DisheveledDev/SPIConputer/system/audio.c

/* audio.c — see audio.h */
#include "audio.h"

#include <math.h>
#include "mod.h"
#include <stdlib.h>
#include <string.h>

audio_state_t *g_current_audio;

/* ------------------------------------------------------------------ */
/* Fixed-point tables (built once, using double math)                  */
/* ------------------------------------------------------------------ */

enum { AUDIO_BLOCK = 64 };

static bool s_tables_ready;
static uint32_t s_note_inc[128];   /* tone phase increment, Q32/sample */
static uint64_t s_pitch_q32[128];  /* 2^((n-60)/12), Q32 (sample pitch) */
static int16_t s_sine[256];
static uint32_t s_cent_q16[100];   /* 2^(c/1200), Q16: a fraction of a semitone */

static void build_tables(void) {
    if (s_tables_ready) {
        return;
    }
    for (int n = 0; n < 128; n++) {
        double freq = 440.0 * pow(2.0, (n - 69) / 12.0);
        s_note_inc[n] =
            (uint32_t)llround(freq / AUDIO_SAMPLE_RATE * 4294967296.0);
        s_pitch_q32[n] = (uint64_t)llround(pow(2.0, (n - 60) / 12.0) * 4294967296.0);
    }
    for (int i = 0; i < 256; i++) {
        s_sine[i] = (int16_t)lround(sin(2.0 * 3.14159265358979323846 * i / 256.0) *
                                    32767.0);
    }
    for (int c = 0; c < 100; c++) {
        s_cent_q16[c] = (uint32_t)llround(pow(2.0, c / 1200.0) * 65536.0);
    }
    s_tables_ready = true;
}

static uint64_t ms_to_frames(uint32_t ms) {
    return (uint64_t)ms * AUDIO_SAMPLE_RATE / 1000u;
}

/* ------------------------------------------------------------------ */
/* Note names                                                          */
/* ------------------------------------------------------------------ */

int audio_note_parse(const char *name) {
    if (!name || !name[0]) {
        return -1;
    }
    char c = name[0];
    if (c >= 'a' && c <= 'g') {
        c = (char)(c - 'a' + 'A');
    }
    static const int base[7] = {9, 11, 0, 2, 4, 5, 7}; /* A B C D E F G */
    if (c < 'A' || c > 'G') {
        return -1;
    }
    int i = 1;
    int semitone = base[c - 'A'];
    if (name[i] == '#') {
        semitone++;
        i++;
    } else if (name[i] == 'b') {
        semitone--;
        i++;
    }
    if (!name[i]) {
        return -1;
    }
    int sign = 1;
    if (name[i] == '-') {
        sign = -1;
        i++;
    }
    if (name[i] < '0' || name[i] > '9') {
        return -1;
    }
    int octave = name[i] - '0';
    i++;
    if (name[i] >= '0' && name[i] <= '9') {
        octave = octave * 10 + (name[i] - '0');
        i++;
    }
    if (name[i] != '\0') {
        return -1;
    }
    octave *= sign;
    int midi = (octave + 1) * 12 + semitone;
    if (midi < 0 || midi > 127) {
        return -1;
    }
    return midi;
}

/* ------------------------------------------------------------------ */
/* State lifetime                                                      */
/* ------------------------------------------------------------------ */

/* Analyser bands: two-pole resonators y = c1*y1 - c2*y2 + g*x at a
 * quarter of the sample rate (11025 Hz), Q of 2.5, unity gain at the
 * centre; Q14. Computed offline: w = 2*pi*fc/fs, r = exp(-pi*fc/(2.5*fs)),
 * c1 = 2*r*cos(w), c2 = r*r, g = (1-r)*sqrt(1 - 2*r*cos(2w) + r*r). */
const uint16_t audio_spectrum_hz[AUDIO_SPECTRUM_BANDS] = {
    60, 100, 160, 250, 400, 630, 1000, 1600, 2500, 4000,
};
static const int32_t s_spec_coef[AUDIO_SPECTRUM_BANDS][3] = {
    {32526, 16161, 8},     {32344, 16015, 21},   {32042, 15797, 54},
    {31525, 15476, 130},   {30498, 14956, 324},  {28553, 14192, 774},
    {24617, 13044, 1809},  {16719, 11377, 3969}, {3586, 9266, 7043},
    {-13520, 6583, 7577},
};

void audio_state_init(audio_state_t *a) {
    memset(a, 0, sizeof(*a));
    a->master = AUDIO_DEFAULT_VOLUME;
    for (int b = 0; b < AUDIO_SPECTRUM_BANDS; b++) {
        a->spec_c1[b] = s_spec_coef[b][0];
        a->spec_c2[b] = s_spec_coef[b][1];
        a->spec_g[b] = s_spec_coef[b][2];
    }
    build_tables();
}

void audio_spectrum(const audio_state_t *a, uint8_t out[AUDIO_SPECTRUM_BANDS]) {
    for (int b = 0; b < AUDIO_SPECTRUM_BANDS; b++) {
        /* Music spreads over the bands, so a band rarely nears the
         * full-scale-sine peak: four times the raw level (a centred
         * full-scale tone saturates) less a floor that hides the low
         * bands' rounding ripple. */
        uint32_t v = a ? a->spec_level[b] : 0;
        v = v > 512 ? (v - 512) >> 5 : 0;
        out[b] = (uint8_t)(v > 255 ? 255 : v);
    }
}

/* One decimated frame through the resonators (producer). */
static inline void spectrum_feed(audio_state_t *a, int32_t x) {
    for (int b = 0; b < AUDIO_SPECTRUM_BANDS; b++) {
        int32_t y = (int32_t)(((int64_t)a->spec_c1[b] * a->spec_y1[b] -
                               (int64_t)a->spec_c2[b] * a->spec_y2[b] +
                               (int64_t)a->spec_g[b] * x) >> 14);
        a->spec_y2[b] = a->spec_y1[b];
        a->spec_y1[b] = y;
        if (y < 0) y = -y;
        if (y > a->spec_peak[b]) a->spec_peak[b] = y;
    }
}

/* End of a block: the levels take the block's peaks and decay by 1/32
 * a block (about 50 ms to fall by two thirds), so a reader polling a
 * few times a frame sees an envelope, not the odd sample. */
static inline void spectrum_block(audio_state_t *a) {
    for (int b = 0; b < AUDIO_SPECTRUM_BANDS; b++) {
        int32_t lvl = a->spec_level[b];
        lvl -= lvl >> 5;
        int32_t peak = a->spec_peak[b] > 32767 ? 32767 : a->spec_peak[b];
        if (peak > lvl) lvl = peak;
        a->spec_level[b] = (uint16_t)lvl;
        a->spec_peak[b] = 0;
    }
}

void audio_state_free(audio_state_t *a) {
    free(a->sample_pool);
    a->sample_pool = NULL;
    mod_free(a->mod);
    a->mod = NULL;
}

void audio_service(void) {
    audio_state_t *a = g_current_audio;
    if (a && a->mod) {
        mod_service(a->mod);
    }
}

bool audio_sound_defined(const audio_state_t *a, int sound) {
    if (sound < 0) {
        return false;
    }
    if (sound < AUDIO_INSTRUMENT_MAX) {
        return a->instruments[sound].defined != 0;
    }
    if (sound < AUDIO_INSTRUMENT_MAX + AUDIO_SAMPLE_MAX) {
        return a->samples[sound - AUDIO_INSTRUMENT_MAX].defined != 0;
    }
    if (sound >= AUDIO_PRESET_BASE && sound < AUDIO_PRESET_BASE + audio_preset_count()) {
        return true;
    }
    return false;
}

const audio_instrument_t *audio_instrument(const audio_state_t *a, int sound) {
    if (sound >= 0 && sound < AUDIO_INSTRUMENT_MAX) {
        return a->instruments[sound].defined ? &a->instruments[sound] : NULL;
    }
    if (sound >= AUDIO_PRESET_BASE && sound < AUDIO_PRESET_BASE + audio_preset_count()) {
        return &audio_preset(sound - AUDIO_PRESET_BASE)->ins;
    }
    return NULL;
}

static inline bool is_sample(int sound) {
    return sound >= AUDIO_INSTRUMENT_MAX && sound < AUDIO_INSTRUMENT_MAX + AUDIO_SAMPLE_MAX;
}

/* ------------------------------------------------------------------ */
/* Playback requests (core 1 side)                                     */
/* ------------------------------------------------------------------ */

void audio_play_score(audio_state_t *a, int score, int loop) {
    if (score < 0 || score >= AUDIO_SCORE_MAX) {
        return;
    }
    a->req_score = (uint8_t)score;
    a->req_loop = loop < 0 ? a->scores[score].loop : (uint8_t)(loop != 0);
    a->req_play = 1;
}

void audio_stop_score(audio_state_t *a) {
    a->req_stop = 1;
}

bool audio_score_playing(const audio_state_t *a) {
    if (a->req_stop) {
        return false;
    }
    return a->score_active != 0 || a->req_play != 0;
}

int audio_trigger(audio_state_t *a, int sound, int note, int volume, int pan,
                  int dur_ms) {
    if (!audio_sound_defined(a, sound)) {
        return -1;
    }
    unsigned head = atomic_load_explicit(&a->trig_head, memory_order_relaxed);
    unsigned tail = atomic_load_explicit(&a->trig_tail, memory_order_acquire);
    if ((head + 1) % AUDIO_ONESHOT_VOICES == tail) {
        return -1; /* ring full */
    }
    int slot = (int)head;
    audio_trigger_t *t = &a->trig[slot];
    t->sound = (uint8_t)sound;
    t->note = (uint8_t)(note < 0 ? 0 : (note > 127 ? 127 : note));
    t->volume = (uint8_t)(volume < 0 ? 0 : (volume > 255 ? 255 : volume));
    t->pan = (int8_t)(pan < -64 ? -64 : (pan > 63 ? 63 : pan));
    t->dur_ms = (uint16_t)(dur_ms < 0 ? 0 : (dur_ms > 65535 ? 65535 : dur_ms));
    atomic_store_explicit(&a->trig_head,
                          (head + 1) % AUDIO_ONESHOT_VOICES,
                          memory_order_release);
    return slot;
}

void audio_stop_voice(audio_state_t *a, int slot) {
    if (slot < 0 || slot >= AUDIO_ONESHOT_VOICES) {
        return;
    }
    a->stop_flags[slot] = 1;
}

void audio_stop_all_voices(audio_state_t *a) {
    for (int i = 0; i < AUDIO_ONESHOT_VOICES; i++) {
        a->stop_flags[i] = 1;
    }
}

void audio_pause(audio_state_t *a) {
    for (int i = 0; i < AUDIO_VOICES; i++) {
        a->voices[i].active = 0;
        a->voices[i].env_state = AUDIO_ENV_OFF;
    }
    mod_pause(a->mod);
}

/* ------------------------------------------------------------------ */
/* Voice triggering                                                    */
/* ------------------------------------------------------------------ */

static const audio_instrument_t s_sample_envelope = {
    .defined = 1,
    .wave = AUDIO_WAVE_SINE,
    .duty = AUDIO_DEFAULT_DUTY,
    .attack_ms = 0,
    .decay_ms = 0,
    .sustain = 255,
    .release_ms = 20,
    .volume = 255,
    .cutoff = AUDIO_CUTOFF_OPEN,
};

static uint32_t oneshot_hold(const audio_instrument_t *ins, uint32_t dur_ms) {
    if (dur_ms > 0) {
        return (uint32_t)ms_to_frames(dur_ms);
    }
    return (uint32_t)(ms_to_frames(ins->attack_ms) + ms_to_frames(ins->decay_ms));
}

uint32_t audio_oneshot_frames(const audio_instrument_t *ins) {
    return (uint32_t)(ms_to_frames(ins->attack_ms) + ms_to_frames(ins->decay_ms));
}

static void env_enter_decay(audio_voice_t *v, const audio_instrument_t *ins) {
    v->env_sustain = (int32_t)ins->sustain * 256;
    uint32_t df = (uint32_t)ms_to_frames(ins->decay_ms);
    if (df == 0 || v->env_level <= v->env_sustain) {
        v->env_level = v->env_sustain;
        v->env_state = AUDIO_ENV_SUSTAIN;
        return;
    }
    v->env_state = AUDIO_ENV_DECAY;
    v->env_rate = (v->env_level - v->env_sustain) / (int32_t)df;
    if (v->env_rate < 1) {
        v->env_rate = 1;
    }
}

static void env_enter_release(audio_voice_t *v, const audio_instrument_t *ins) {
    uint32_t rf = (uint32_t)ms_to_frames(ins->release_ms);
    v->env_state = AUDIO_ENV_RELEASE;
    if (rf == 0 || v->env_level <= 0) {
        v->env_level = 0;
        v->env_state = AUDIO_ENV_OFF;
        v->active = 0;
        return;
    }
    v->env_rate = v->env_level / (int32_t)rf;
    if (v->env_rate < 1) {
        v->env_rate = 1;
    }
}

static void voice_start_tone(audio_voice_t *v, const audio_instrument_t *ins,
                             int note, uint32_t hold) {
    memset(v, 0, sizeof(*v));
    v->active = 1;
    v->source = 0;
    v->note = (uint8_t)note;
    v->inc = s_note_inc[note & 0x7f];
    v->lfsr = (uint16_t)(0x4001 | (note << 4));
    v->hold_frames = hold;
    v->env_sustain = (int32_t)ins->sustain * 256;

    uint32_t af = (uint32_t)ms_to_frames(ins->attack_ms);
    if (af == 0) {
        v->env_level = 65536;
        env_enter_decay(v, ins);
    } else {
        v->env_state = AUDIO_ENV_ATTACK;
        v->env_rate = 65536 / (int32_t)af;
        if (v->env_rate < 1) {
            v->env_rate = 1;
        }
    }
}

static void voice_start_sample(audio_voice_t *v, const audio_pcm_t *smp,
                               int note, uint32_t hold) {
    memset(v, 0, sizeof(*v));
    v->active = 1;
    v->source = 1;
    v->note = (uint8_t)note;
    /* s_pitch_q32[n] is 2^((n-60)/12): the shift from the root note. */
    int root = smp->root ? smp->root : 60;
    int shift = 60 + (note & 0x7f) - root;
    if (shift < 0) shift = 0;
    if (shift > 127) shift = 127;
    v->step = ((uint64_t)smp->rate * s_pitch_q32[shift]) / AUDIO_SAMPLE_RATE;
    v->hold_frames = hold;
    v->env_sustain = 65536;
    v->env_level = 65536;
    v->env_state = AUDIO_ENV_SUSTAIN;
}

static void voice_apply_mix(audio_voice_t *v, int volume, int pan) {
    if (volume < 0) volume = 0;
    if (volume > 255) volume = 255;
    if (pan < -64) pan = -64;
    if (pan > 63) pan = 63;
    v->volume = (uint8_t)volume;
    int lg = pan >= 63 ? 0 : 255 - (pan > 0 ? pan * 4 : 0);
    int rg = pan <= -64 ? 0 : 255 + (pan < 0 ? pan * 4 : 0);
    v->lgain = (uint8_t)(lg < 0 ? 0 : (lg > 255 ? 255 : lg));
    v->rgain = (uint8_t)(rg < 0 ? 0 : (rg > 255 ? 255 : rg));
}

/* Trigger `sound` into voice `idx`. dur_ms 0 = one-shot envelope. */
static void trigger_voice(audio_state_t *a, int idx, int sound, int note,
                          int volume, int pan, int dur_ms) {
    if (idx < 0 || idx >= AUDIO_VOICES || !audio_sound_defined(a, sound)) {
        return;
    }
    audio_voice_t *v = &a->voices[idx];
    if (!is_sample(sound)) {
        const audio_instrument_t *ins = audio_instrument(a, sound);
        voice_start_tone(v, ins, note, oneshot_hold(ins, (uint32_t)dur_ms));
        v->sound = (uint8_t)sound;
        voice_apply_mix(v, (ins->volume * volume) >> 8, pan);
    } else {
        const audio_pcm_t *smp = &a->samples[sound - AUDIO_INSTRUMENT_MAX];
        /* Until the sample ends; a looped one would never, so a play
         * without a length gets the one-shot tail before its release. */
        uint32_t hold = dur_ms > 0 ? (uint32_t)ms_to_frames((uint32_t)dur_ms)
                                   : (smp->loop_len ? (uint32_t)ms_to_frames(AUDIO_ONESHOT_TAIL_MS)
                                                    : 0xFFFFFFFFu);
        voice_start_sample(v, smp, note, hold);
        v->sound = (uint8_t)sound;
        voice_apply_mix(v, (s_sample_envelope.volume * volume) >> 8, pan);
    }
}

/* ------------------------------------------------------------------ */
/* Request servicing + score scheduling (producer side)                */
/* ------------------------------------------------------------------ */

static void score_stop_voices(audio_state_t *a) {
    for (int c = 0; c < AUDIO_CHANNELS; c++) {
        a->voices[c].active = 0;
        a->voices[c].env_state = AUDIO_ENV_OFF;
    }
}

static void schedule_block(audio_state_t *a, int n) {
    const audio_score_t *sc = &a->scores[a->score_index];
    uint32_t block_end = a->score_frame + (uint32_t)n;
    for (int c = 0; c < AUDIO_CHANNEL_MAX; c++) {
        const audio_channel_t *ch = &sc->ch[c];
        uint16_t i = a->ch_next[c];
        while (i < ch->count) {
            const audio_event_t *ev = &a->events[ch->start + i];
            if (ms_to_frames(ev->time_ms) >= block_end) {
                break;
            }
            trigger_voice(a, c, ev->sound, ev->note, ev->volume, ev->pan,
                          (int)ev->dur_ms);
            i++;
        }
        a->ch_next[c] = i;
    }
}

static void apply_requests(audio_state_t *a) {
    if (a->req_stop) {
        a->req_stop = 0;
        a->score_active = 0;
        score_stop_voices(a);
    }
    if (a->req_play) {
        a->req_play = 0;
        if (a->req_score < AUDIO_SCORE_MAX && a->scores[a->req_score].valid) {
            score_stop_voices(a);
            if (a->mod) a->mod->playing = 0; /* one tune at a time */
            a->score_index = a->req_score;
            a->score_loop = a->req_loop;
            a->score_frame = 0;
            for (int c = 0; c < AUDIO_CHANNEL_MAX; c++) {
                a->ch_next[c] = 0;
            }
            a->score_active = 1;
        }
    }
    for (int s = 0; s < AUDIO_ONESHOT_VOICES; s++) {
        if (a->stop_flags[s]) {
            a->stop_flags[s] = 0;
            audio_voice_t *v = &a->voices[AUDIO_CHANNELS + s];
            v->active = 0;
            v->env_state = AUDIO_ENV_OFF;
        }
    }
    unsigned tail = atomic_load_explicit(&a->trig_tail, memory_order_relaxed);
    unsigned head = atomic_load_explicit(&a->trig_head, memory_order_acquire);
    while (tail != head) {
        const audio_trigger_t *t = &a->trig[tail];
        trigger_voice(a, AUDIO_CHANNELS + (int)tail, t->sound, t->note, t->volume,
                      t->pan, t->dur_ms);
        tail = (tail + 1) % AUDIO_ONESHOT_VOICES;
    }
    atomic_store_explicit(&a->trig_tail, tail, memory_order_release);
}

/* ------------------------------------------------------------------ */
/* Pitch effects (control rate: once per AUDIO_BLOCK frames per voice)   */
/* ------------------------------------------------------------------ */

/* The phase increment for a pitch in cents (0 = C-1, 12700 = G9),
 * clamped to the note table's range. */
static uint32_t inc_for_cents(int32_t cents) {
    if (cents < 0) cents = 0;
    if (cents > 127 * 100) cents = 127 * 100;
    int note = cents / 100;
    int frac = cents % 100;
    return (uint32_t)(((uint64_t)s_note_inc[note] * s_cent_q16[frac]) >> 16);
}

/* Recompute a tone voice's pitch from its note and the instrument's
 * slide, vibrato and arpeggio at the voice's age. */
static void voice_control(audio_voice_t *v, const audio_instrument_t *ins) {
    if (ins->wave == AUDIO_WAVE_NOISE && ins->slide == 0) {
        return; /* noise pitch is fixed unless it slides */
    }
    if (ins->slide == 0 && ins->vib_depth == 0 && ins->arp_ms == 0) {
        return; /* plain note: the trigger's increment stands */
    }
    int32_t cents = (int32_t)v->note * 100;
    uint32_t age_ms = (uint32_t)((uint64_t)v->age * 1000u / AUDIO_SAMPLE_RATE);
    if (ins->slide != 0) {
        cents += (int32_t)ins->slide * (int32_t)age_ms / 10; /* semitones/s * ms / 1000 * 100 */
    }
    if (ins->arp_ms != 0) {
        uint32_t step = age_ms / ins->arp_ms;
        int8_t offsets[3] = {0, ins->arp, ins->arp2};
        int steps = ins->arp2 != 0 ? 3 : 2;
        if (ins->arp_loop) {
            cents += (int32_t)offsets[step % (uint32_t)steps] * 100;
        } else if (step >= 1) {
            cents += (int32_t)offsets[step >= (uint32_t)steps ? steps - 1 : (int)step] * 100;
        }
    }
    if (ins->vib_depth != 0) {
        /* vib_rate is tenths of a Hz; the phase advances per control block. */
        uint32_t per_block = (uint32_t)ins->vib_rate * 65536u * AUDIO_BLOCK / (10u * AUDIO_SAMPLE_RATE);
        v->vib_phase = (uint16_t)(v->vib_phase + per_block);
        cents += ((int32_t)s_sine[v->vib_phase >> 8] * ins->vib_depth) / 32767;
    }
    v->inc = inc_for_cents(cents);
}

/* One-pole low-pass for the `cutoff` tone control: 255 is open (no
 * filtering), lower values roll the top off. */
static inline int32_t lowpass(audio_voice_t *v, int32_t x, uint8_t cutoff) {
    if (cutoff == 0 || cutoff >= AUDIO_CUTOFF_OPEN) {
        return x; /* 0: unset, as good as open */
    }
    /* k from 1/256 (very dark) to about 3/4 of the way to open. */
    int32_t k = 1 + ((int32_t)cutoff * (int32_t)cutoff) / 340;
    v->lp += ((x - v->lp) * k) >> 8;
    return v->lp;
}

/* ------------------------------------------------------------------ */
/* Mixer                                                               */
/* ------------------------------------------------------------------ */

static inline int32_t tone_sample(const audio_voice_t *v,
                                  const audio_instrument_t *ins) {
    uint32_t p16 = v->phase >> 16;
    switch (ins->wave) {
    case AUDIO_WAVE_SQUARE:
        return p16 < (uint32_t)ins->duty * 4096u ? 32767 : -32768;
    case AUDIO_WAVE_TRIANGLE: {
        uint32_t idx = v->phase >> 24; /* 0..255 */
        int32_t s = idx < 128 ? (int32_t)idx * 2 - 128 : (int32_t)(255 - idx) * 2 - 128;
        return s * 256;
    }
    case AUDIO_WAVE_SAW:
        return (int32_t)p16 - 32768;
    case AUDIO_WAVE_SINE:
    default:
        return s_sine[v->phase >> 24];
    }
}

/* Advance the noise LFSR once per waveform period. */
static inline int32_t noise_sample(audio_voice_t *v) {
    uint32_t before = v->phase;
    v->phase += v->inc;
    if (v->phase < before) {
        uint16_t l = v->lfsr;
        v->lfsr = (uint16_t)((l >> 1) | (((l ^ (l >> 1)) & 1) << 14));
    }
    return (v->lfsr & 1) ? 32767 : -32768;
}

static inline void mix_frame(audio_state_t *a, int16_t *out) {
    int32_t l = 0, r = 0;
    for (int i = 0; i < AUDIO_VOICES; i++) {
        audio_voice_t *v = &a->voices[i];
        if (!v->active) {
            continue;
        }

        int32_t e_l, e_r;
        if (v->source == 0) {
            const audio_instrument_t *inst = audio_instrument(a, v->sound);
            if (!inst) {
                v->active = 0;
                continue;
            }
            if ((v->age & (AUDIO_BLOCK - 1)) == 0) {
                voice_control(v, inst);
            }
            v->age++;
            int32_t s;
            if (inst->wave == AUDIO_WAVE_NOISE) {
                s = noise_sample(v);
            } else {
                s = tone_sample(v, inst);
                v->phase += v->inc;
            }
            s = lowpass(v, s, inst->cutoff);
            e_l = e_r = (s * v->env_level) >> 16;
        } else {
            const audio_pcm_t *smp = &a->samples[v->sound - AUDIO_INSTRUMENT_MAX];
            uint64_t end = (uint64_t)smp->frames << 32;
            if (smp->loop_len) {
                /* Sustain: wrap into the loop until the release ends. */
                uint64_t loop_end = ((uint64_t)smp->loop_start + smp->loop_len) << 32;
                while (v->pos >= loop_end) {
                    v->pos -= (uint64_t)smp->loop_len << 32;
                }
            } else if (v->pos >= end) {
                v->active = 0;
                v->env_state = AUDIO_ENV_OFF;
                continue;
            }
            uint32_t idx = (uint32_t)(v->pos >> 32);
            uint32_t frac = (uint32_t)(v->pos & 0xffffffffu);
            const int16_t *base =
                a->sample_pool + smp->offset / 2 + (size_t)idx * smp->channels;
            int32_t c0 = base[0];
            int32_t c1 = (idx + 1 < smp->frames) ? base[smp->channels] : c0;
            int32_t s0 = c0 + (int32_t)(((int64_t)(c1 - c0) * frac) >> 32);
            if (smp->channels == 2) {
                int32_t d0 = base[1];
                int32_t d1 = (idx + 1 < smp->frames) ? base[3] : d0;
                int32_t s1 = d0 + (int32_t)(((int64_t)(d1 - d0) * frac) >> 32);
                e_l = (s0 * v->env_level) >> 16;
                e_r = (s1 * v->env_level) >> 16;
            } else {
                e_l = e_r = (s0 * v->env_level) >> 16;
            }
            v->pos += v->step;
        }

        e_l = (e_l * v->volume) >> 8;
        e_r = (e_r * v->volume) >> 8;
        l += (e_l * v->lgain) >> 8;
        r += (e_r * v->rgain) >> 8;

        /* Envelope + hold timer. */
        const audio_instrument_t *ins =
            v->source == 0 ? audio_instrument(a, v->sound) : &s_sample_envelope;
        if (v->hold_frames != 0xFFFFFFFFu && v->env_state != AUDIO_ENV_OFF) {
            if (v->hold_frames > 0) {
                v->hold_frames--;
            }
            if (v->hold_frames == 0 && v->env_state != AUDIO_ENV_RELEASE) {
                env_enter_release(v, ins);
            }
        }
        switch (v->env_state) {
        case AUDIO_ENV_ATTACK:
            v->env_level += v->env_rate;
            if (v->env_level >= 65536) {
                v->env_level = 65536;
                env_enter_decay(v, ins);
            }
            break;
        case AUDIO_ENV_DECAY:
            v->env_level -= v->env_rate;
            if (v->env_level <= v->env_sustain) {
                v->env_level = v->env_sustain;
                v->env_state = AUDIO_ENV_SUSTAIN;
            }
            break;
        case AUDIO_ENV_RELEASE:
            v->env_level -= v->env_rate;
            if (v->env_level <= 0) {
                v->env_level = 0;
                v->env_state = AUDIO_ENV_OFF;
                v->active = 0;
            }
            break;
        default:
            break;
        }
    }

    mod_mix_frame(a->mod, &l, &r);

    if (++a->spec_phase >= 4) {
        a->spec_phase = 0;
        spectrum_feed(a, (l + r) >> 1);
    }

    int32_t master = a->master;
    l = (l * master) >> 8;
    r = (r * master) >> 8;
    if (l > 32767) l = 32767;
    if (l < -32768) l = -32768;
    if (r > 32767) r = 32767;
    if (r < -32768) r = -32768;
    out[0] = (int16_t)l;
    out[1] = (int16_t)r;
}

void audio_mix(audio_state_t *a, int16_t *out, int frames) {
    if (!a || frames <= 0) {
        if (out && frames > 0) {
            memset(out, 0, (size_t)frames * 2 * sizeof(int16_t));
        }
        return;
    }
    apply_requests(a);

    int done = 0;
    while (done < frames) {
        int n = frames - done;
        if (n > AUDIO_BLOCK) {
            n = AUDIO_BLOCK;
        }
        if (a->score_active) {
            schedule_block(a, n);
        }
        if (a->mod) {
            mod_advance(a->mod, n);
        }
        for (int i = 0; i < n; i++) {
            mix_frame(a, out + (size_t)(done + i) * 2);
        }
        spectrum_block(a);
        if (a->score_active) {
            a->score_frame += (uint32_t)n;
            const audio_score_t *sc = &a->scores[a->score_index];
            uint32_t len = (uint32_t)ms_to_frames(sc->length_ms);
            if (a->score_frame >= len) {
                if (a->score_loop && len > 0) {
                    a->score_frame -= len;
                    for (int c = 0; c < AUDIO_CHANNEL_MAX; c++) {
                        a->ch_next[c] = 0;
                    }
                } else {
                    a->score_active = 0;
                }
            }
        }
        done += n;
    }
}
