DisheveledDev/SPIConputer/system/program.h

/* program.h
 *
 * Process model (Phase 5): a stack of Lua programs, each with its own
 * lua_State (capped heap), screen slot, timer list and input event
 * ring. The scheduler loop (driven from core 1) drains core 0's input
 * queue into the top program, runs due timers, otherwise calls tick().
 *
 * Ticks and timer callbacks never overlap: one scheduler step runs
 * either the due timers or one tick. A throwing tick or timer callback
 * terminates the program (finish() runs) and the parent resumes.
 */
#pragma once

#include <stdbool.h>
#include <stdint.h>

#include "lua.h"
#include "audio.h"
#include "input.h"
#include "video.h"

#define PROGRAM_MAX 4
/* Per-program Lua heap cap. The shell alone needs ~45 KB on the device
 * once loaded (79 KB on a 64-bit host, where Lua's structs are larger),
 * so 64 KB left no room for its APPS picker; 96 KB keeps a shell + one
 * app well inside the ~290 KB heap. Overridable per build. */
#ifndef PROGRAM_HEAP_CAP
#define PROGRAM_HEAP_CAP (96u * 1024u)
#endif
#define PROGRAM_TIMER_MAX 8
#define PROGRAM_EVENT_DEPTH 128
#define PROGRAM_ARG_MAX 16 /* Execute/ExecuteString argument cap */

typedef struct {
    bool used;
    bool oneshot;
    uint32_t interval_ms;
    uint64_t deadline_us; /* absolute (os_time_us) */
    int fn_ref;           /* Lua registry ref to the callback */
} program_timer_t;

typedef struct program_s {
    /* -- lifetime -- */
    bool used;
    uint32_t pid;
    char name[260];
    lua_State *L;
    int chunk_ref;     /* registry ref to the program chunk (kept alive) */
    int setup_ref;     /* LUA_NOREF when absent */
    int tick_ref;
    int finish_ref;
    /* The optional input callbacks (globals "on_keypress"/"on_control")
     * are looked up at dispatch time, not cached here, so a program or a
     * framework can install or replace them after load (e.g. in setup). */
    bool exit_requested;
    /* Set when a Launch(..., replace) has taken this program's place:
     * it is still inside its own Lua frame until that call returns, and
     * the screen now belongs to the new program, so its Screen* calls
     * are ignored (screen_lua.c) until it is reaped. */
    bool replaced;
    bool interactive;
    bool requires_video;
    bool requires_audio;
    /* Utility result (UtilityResult): a message or a table serialised
     * as Lua source, malloc'd; ownership moves to the parent's
     * child_result_* when the utility exits, and UtilityPoll frees it. */
    bool utility_result_set;
    bool utility_ok;
    char *utility_output;
    bool utility_is_table;
    bool child_result_pending;
    bool child_result_ok;
    char *child_result_output;
    bool child_result_is_table;
    bool scheduler_started;
    char cwd[260];

    /* -- heap budget -- */
    size_t heap_used;
    size_t heap_cap;

    /* -- screen slot --
     * The display state lives on core 0 (video.h); a program's slot is
     * its index in the pool below, selected via a queued op on launch
     * and on exit. Needs no memory here. */

    /* -- audio state (heap-allocated like the screen used to be) -- */
    audio_state_t *audio;

    /* -- timers -- */
    program_timer_t timers[PROGRAM_TIMER_MAX];
    bool paused;
    uint64_t pause_start_us; /* valid while paused */

    /* WaitVSync bookkeeping: the frame counter at this program's last
     * WaitVSync call, so each call reports the frames elapsed since. */
    uint32_t vsync_last_frames;

    /* -- input event ring (core 1 only, no atomics needed) -- */
    input_event_t events[PROGRAM_EVENT_DEPTH];
    uint32_t ev_head; /* push here */
    uint32_t ev_tail; /* pop here */
    uint8_t joy[2];   /* current joystick bitmasks (INPUT_DIR_*) */

    struct program_s *next; /* parent program below on the stack */
} program_t;

/* One-time init (zeroes the pool). */
void program_init(void);

/* Boot the first program (the shell). Returns false on load failure.
 * `arg` (optional) is passed to the program chunk as its first vararg. */
bool program_boot(const char *path, const char *arg);

/* One scheduler iteration: drain input, run due timers, else tick. */
void program_scheduler_step(void);

/* Current top program (NULL when the stack is empty). */
program_t *program_top(void);

/* Launch `path` as a new program, pausing the current one. Returns 0
 * on success; on failure writes a message to *err and the current
 * program keeps running. `arg` (optional) is passed to the program
 * chunk as its first vararg. */
int program_launch(const char *path, const char *arg, const char **err);

/* Launch `path` in place of the current program: the caller leaves the
 * stack (its parent becomes the new program's parent) and its Lua
 * state, timers and audio state are released once the call that
 * launched it returns (the caller may finish its current function; it
 * is never ticked again). A boot loader uses this to hand the machine
 * over to the shell without staying resident. */
int program_launch_replace(const char *path, const char *arg, const char **err);

/* Foreground launch of a program file with `argc` (<= PROGRAM_ARG_MAX)
 * arguments. The arguments are exposed to the program as the global
 * `args` table (1-based); argv[0] is also the chunk's first vararg. */
int program_launch_args(const char *path, const char *const *argv, int argc,
                        const char **err);

/* Foreground launch of a Lua source string (ExecuteString). `name` is
 * used in error messages; the arguments follow the same rules as
 * program_launch_args(). */
int program_launch_source(const char *name, const char *source, size_t len,
                          const char *const *argv, int argc,
                          const char **err);

/* Ask the current program to exit after its tick returns. */
void program_exit_request(void);

/* Retrieve and clear a completed noninteractive utility result. */
bool program_utility_result(program_t *p, bool *ok, const char **output);

/* Call the given registry-ref function under pcall. Returns false on
 * a Lua error (message pushed on the stack). */
bool program_pcall(program_t *p, int fn_ref);

/* Time spent inside Lua (every tick, timer and input callback, setup
 * and finish) since the last reset: the numbers the bring-up log prints
 * once per period, so a slow tick or a GC stall shows up as a max.
 * `reset` clears the window after copying it out. */
typedef struct {
    uint32_t calls;
    uint64_t total_us;
    uint32_t min_us;
    uint32_t max_us;
} program_lua_stats_t;
void program_lua_stats(program_lua_stats_t *out, bool reset);

/* Terminate `p` (run finish(), close state, resume parent). */
void program_terminate(program_t *p);

/* Deferred audio state frees. A terminated program's audio state stays
 * alive until the audio path is done with it; the retire queue parks it
 * for two frame boundaries first. program_retire_reap() runs once per
 * scheduler step (it also accepts a synthetic count in the host tests). */
void program_retire_reap(uint32_t frame_count);
int program_retire_pending(void);

/* Input event ring (core 1 only). */
void program_event_push(program_t *p, const input_event_t *ev);
bool program_event_pop(program_t *p, input_event_t *ev);

/* Timers. Returns the timer id (>= 1) or 0 when the list is full. */
int program_timer_create(program_t *p, int fn_ref, uint32_t interval_ms,
                         bool oneshot);
bool program_timer_stop(program_t *p, int id);

/* Fetch `path` from the SD card into a malloc'd buffer (via RPC).
 * A `*.lua` path prefers its compiled `*.prg` sibling; `resolved`
 * (optional) receives the path actually read. Returns 0 on success;
 * on failure *err gets a static message. */
int program_read_file(const char *path, char **out, size_t *out_len,
                      char *resolved, size_t resolved_size,
                      const char **err);
