DisheveledDev/SPIConputer/system/hw_config.c

/* hw_config.c
 *
 * Hardware configuration for the SD card slot on the SPIComputer.
 * Pin numbers come from board_config.h and follow the selected platform:
 *   - RP2040 dev board: SPI1 SCK=GP10, MOSI=GP11, MISO=GP12, CS=GP13
 *   - RP2354B product:  SPI1 SCK=GP10, MOSI=GP11, MISO=GP8,  CS=GP9
 *     (GP12-15 are HSTX lanes on RP2350, so they cannot carry SPI1).
 */

#include <string.h>
//
#include "pico.h"
#include "my_debug.h"
//
#include "board_config.h"
#include "hw_config.h"
//
#include "ff.h" /* Obtains integer types */
//
#include "diskio.h" /* Declarations of disk functions */

// Hardware Configuration of SPI "objects"
// Note: multiple SD cards can be driven by one SPI if they use different
// slave selects.
static spi_t spis[] = {  // One for each SPI.
    {
        .hw_inst = SD_SPI_INSTANCE,  // SPI component
        .miso_gpio = SD_PIN_MISO,    // GPIO number (not pin number)
        .mosi_gpio = SD_PIN_MOSI,
        .sck_gpio = SD_PIN_SCK,
        .baud_rate = 12500 * 1000,
        // .baud_rate = 25 * 1000 * 1000, // Actual frequency: 20833333.
    }};

// Hardware Configuration of the SD Card "objects"
static sd_card_t sd_cards[] = {  // One for each SD card
    {
        .pcName = "0:",   // Name used to mount device
        .spi = &spis[0],  // Pointer to the SPI driving this card
        .ss_gpio = SD_PIN_CS,  // The SPI slave select GPIO for this SD card
        .use_card_detect = false,
        .card_detect_gpio = -1,  // Card detect (unused)
        .card_detected_true = 1  // What the GPIO read returns when a card is
                                 // present. Use -1 if there is no card detect.
    }};

/* ********************************************************************** */
size_t sd_get_num() { return count_of(sd_cards); }
sd_card_t *sd_get_by_num(size_t num) {
    if (num < sd_get_num()) {
        return &sd_cards[num];
    } else {
        return NULL;
    }
}
size_t spi_get_num() { return count_of(spis); }
spi_t *spi_get_by_num(size_t num) {
    if (num < spi_get_num()) {
        return &spis[num];
    } else {
        return NULL;
    }
}

/* [] END OF FILE */
