DisheveledDev/SPIConputer/system/tests/host/audio_test.c

/* audio_test.c
 *
 * Host-side tests for the Phase 8 audio pieces: the synth engine
 * (oscillators, envelopes, panning, mixing), the score scheduler
 * (timing, release, loop wrap), PCM sample playback, and the Lua
 * sound module (SoundDefine/MusicDefine/... + WAV loading over the
 * mock SD card).
 *
 * Build and run:
 *   cmake -S tests/host -B build-host
 *   cmake --build build-host
 *   ./build-host/spicomputer_audio_tests
 */
#include <math.h>
#include <stdio.h>
#include <stdlib.h>
#include <string.h>

#include "audio.h"
#include "fs_core0.h"
#include "lauxlib.h"
#include "lua.h"
#include "program.h"
#include "rpc.h"
#include "system_state.h"

extern void mock_set_file(const char *path, const char *content);
extern void mock_set_file_bytes(const char *path, const void *data, size_t len);

static int g_failures = 0;

#define CHECK(cond, msg)                                                     \
    do {                                                                     \
        if (!(cond)) {                                                       \
            printf("FAIL: %s (line %d)\n", msg, __LINE__);                   \
            g_failures++;                                                    \
        }                                                                    \
    } while (0)

static void rpc_wait_host(void) {
    fs_core0_service();
}

static void define_square(audio_state_t *a, int id, int release_ms) {
    audio_instrument_t *ins = &a->instruments[id];
    memset(ins, 0, sizeof(*ins));
    ins->defined = 1;
    ins->wave = AUDIO_WAVE_SQUARE;
    ins->duty = 8;
    ins->attack_ms = 0;
    ins->decay_ms = 0;
    ins->sustain = 255;
    ins->release_ms = (uint8_t)release_ms;
    ins->volume = 255;
}

static void add_event(audio_state_t *a, audio_score_t *sc, int ch, int idx,
                      uint32_t at, uint32_t dur, int note) {
    audio_event_t *ev = &a->events[sc->ch[ch].start + idx];
    memset(ev, 0, sizeof(*ev));
    ev->time_ms = at;
    ev->dur_ms = dur;
    ev->sound = 0;
    ev->note = (uint8_t)note;
    ev->volume = 255;
    ev->pan = 0;
}

/* ---------------- test 1: note names ---------------- */

static void test_note_parse(void) {
    CHECK(audio_note_parse("C4") == 60, "C4 = 60");
    CHECK(audio_note_parse("A4") == 69, "A4 = 69");
    CHECK(audio_note_parse("C#4") == 61, "C#4 = 61");
    CHECK(audio_note_parse("Db4") == 61, "Db4 = 61");
    CHECK(audio_note_parse("C-1") == 0, "C-1 = 0");
    CHECK(audio_note_parse("G9") == 127, "G9 = 127");
    CHECK(audio_note_parse("H4") == -1, "H4 invalid");
    CHECK(audio_note_parse("C") == -1, "C invalid");
    CHECK(audio_note_parse("") == -1, "empty invalid");
}

/* ---------------- test 2: square + stereo ---------------- */
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
